ancientcomputing/rc2014/eagle/8085_board/README.md

<b>8085 Processor Board for the RC2014</b>
<p>
Exposes SID/SOD to an FTDI header for UART-less serial.
<p>
Tested. Wiring error between reset RC network and pin 13 of he 74xx14. Fixed in this version.
<p>

<p>
A simple Monitor can be found in the <a href="https://github.com/ancientcomputing/rc2014/tree/master/rom/8085">rom/8085 folder</a>.
<p>
Copyright Ben Chong and licensed freely back to the community.
