ancientcomputing/rc2014/eagle/z80_board/README.md

The board is available from OSH Park at the following link:
<p>

<p>
Copyright Ben Chong and freely licensed back to the community.
