ancientcomputing/rc2014/rom/6502/monitor_ehbasic/README.md

<b>Monitor + EhBASIC ROM</b>
<p>
These are the ROM images that combines the Monitor/Debugger and Enhanced BASIC. This is a 32KB image and can be used to program a 27256 or 28C256. 
<p>
If your ROM address space is only 16KB, you will need to extract the top 16KB of the image to program your device.
<p>
BASIC can be launched by (G)oing to location $c100 from the Monitor. This is the cold start address.
<p>
The BASIC warm start address is at $c103. 
<p>
To return to the Monitor, enter the SYS command.
<p>
<hr>
<p>	
monbas65_16C550.rom : For use with 16550 UART Boards, port address at $c0c0. Will use autoflow control if available. Does not use interrupts with software buffer.
<p>
monbas65_16C550_irq.rom : For use with 16550 UART boards, port address at $c0c0. Does not use autoflow control. Uses interrupts and software buffer.
<p>
monbas65_16c750.rom : For use with 16550 UART RevC board and TI16C750 UART chip (Mouser #1595-TL16C750FN). Uses autoflow control. Does not use interrupts.
<p>
monbas65_6551.rom : For use with 6551 ACIA board. Does not use interrupts. High risk of character overruns at 115200 baud
<p>
monbas65_6850.rom : For use with original RC2014 Serial I/O board with appropriate changes. Does not use interrupts.
<p>
monbas65_rruart.rom : For use with Real Retro UART board. 9600 baud only.
<p>
