ancientcomputing/rc2014/source/z80/rruart/README.md

<b>BIOS for Real Retro UART Board</b>
<p>
This is the BIOS for the Real Retro UART Board using an RCA/Harris CDP6402, AY-3-1015 or similar UART.
<p>
Tested in CPU8080 mode.
