ancientcomputing/rc2014/rom/z80/16x550_revb/README.md

Monitor/Debugger+BASIC for RC2014 system using the 16550 Rev B board.
<p>
The UART port address is c0h instead of 80h.
