ancientcomputing/rc2014/rom/8080_8085/monitor/rruart/README.md

<b>Monitor for 8085 CPU board with Real Retro UART board</b>
<p>
This is the Monitor program for the 8085 CPU Board when using the Real Retro UART Board.
