ancientcomputing/rc2014/eagle/16550_board_rev_b/README.md

16550 UART Board Rev B
<p>
This is the Rev B version of the 16550 UART Board for the RC2014.
<p>
The top 3 changes are:
<br>- Use of port addresses C0H-FFH to avoid collision with the default 68B50 UART
<br>- Use of 74HCT03 open collector gates, particularly to drive the /INT signal line so that it can be shared with other devices that also drive the interrupt line.
<br>- Availability of the 16550's OP1 and OP2 lines to a pin header for general use e.g. to generate an audio signal or page switch RAM/ROM etc.
<p>
This design has been tested with a PC16550CN.
<p>
PCBs are available from OSH Park at:
<p>


<p>
A BIOS will be available soon.
