ancientcomputing/rc2014/eagle/16550_board/README.md

The board has been tested and a BIOS and associated Monitor/Debugger/BASIC binaries released.
<p>
The board is also available from OSH Park at the following link:
<p>

<p>
Note that I do not have any relationship with OSH Park other than that of a customer.
<p>
Copyright Ben Chong and licensed freely back to the community.
