ancientcomputing/rc2014/rom/z80/16x550/README.md

timon.rom - Monitor/Debugger for RC2014 using the 16x550 UART card. Assumes 1.8432MHz oscillator and 115200 baudrate.
<p>
timonbas.rom - Monitor/Debugger+BASIC for RC2014 using the 16x550 UART card. Assumes 1.8432MHz oscillator and 115200 baudrate.
<p>
