ancientcomputing/rc2014/source/6809/bringup/README.MD

Bring-up code for 6809 CPU Board for RC2014.

This code assume the use of the "Real Retro UART" board and will dump a couple of characters ("Ab") to the console.
