ancientcomputing/rc2014/eagle/NSC800_board/rc2014_nsc800.pdf

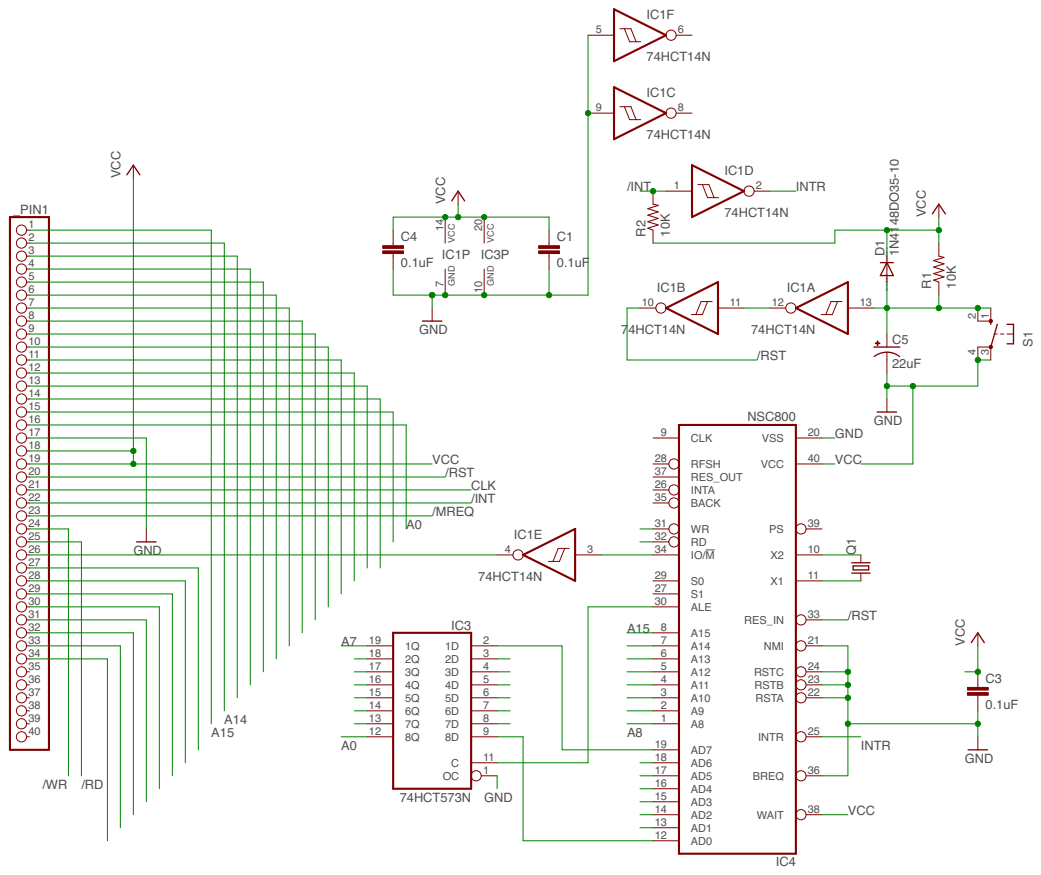
[picture p9: page 1]

SpiceOrder 1 SpiceOrder 2 0.1uF VCC VCC GND 0.1uF VCC GND 0.1uF 22uF 1N4148DO35-10 10K GND VCC 74HCT14N 74HCT14N GND 74HCT14N 74HCT14N 74HCT14N 74HCT14N 74HCT573N 10K NSC800 _PIN1 12345678910111213141516171819202122232425262728293031323334353637383940 C1 C3 C4 S1 3 21 4 C5 D1 R1 IC1A 12 13 IC1B 10 11 IC1PGND VCC 7 14 IC1C 9 8 IC1D 1 2 IC1E 4 3 IC1F 5 6 IC3 OC 1 1D 2 2D 3 3D 4 4D 5 5D 6 6D 7 7D 8 8D 9 C 11 8Q 12 7Q 13 6Q 14 5Q 15 4Q 16 3Q 17 2Q 18 1Q 19 Q1 IC3PGND VCC 10 20 R2 IC4 AD0 12 AD1 13 AD2 14 AD3 15 AD4 16 AD5 17 AD6 18 AD7 19 A8 1 A9 2 A10 3 A11 4 A12 5 A13 6 A14 7 A15 8 ALE 30 S0 29 IO/M 34 RD 32 WR 31 BACK 35 INTA 26 RES_OUT 37 CLK 9 WAIT 38 BREQ 36 INTR 25 RFSH 28 RSTA 22 RSTB 23 RSTC 24 NMI 21 RES_IN 33 X1 11 X2 10 VCC 40 VSS 20 PS 39 S1 27 A7 VCC VCCVCC /RST /RST /RST /INT /INT A0 A0 GND GND /WR A15 A15 A14 A8 CLK /MREQ /RD INTR INTR
