ancientcomputing/rc2014/eagle/rr3kram/rc2014_3kb_ram.pdf

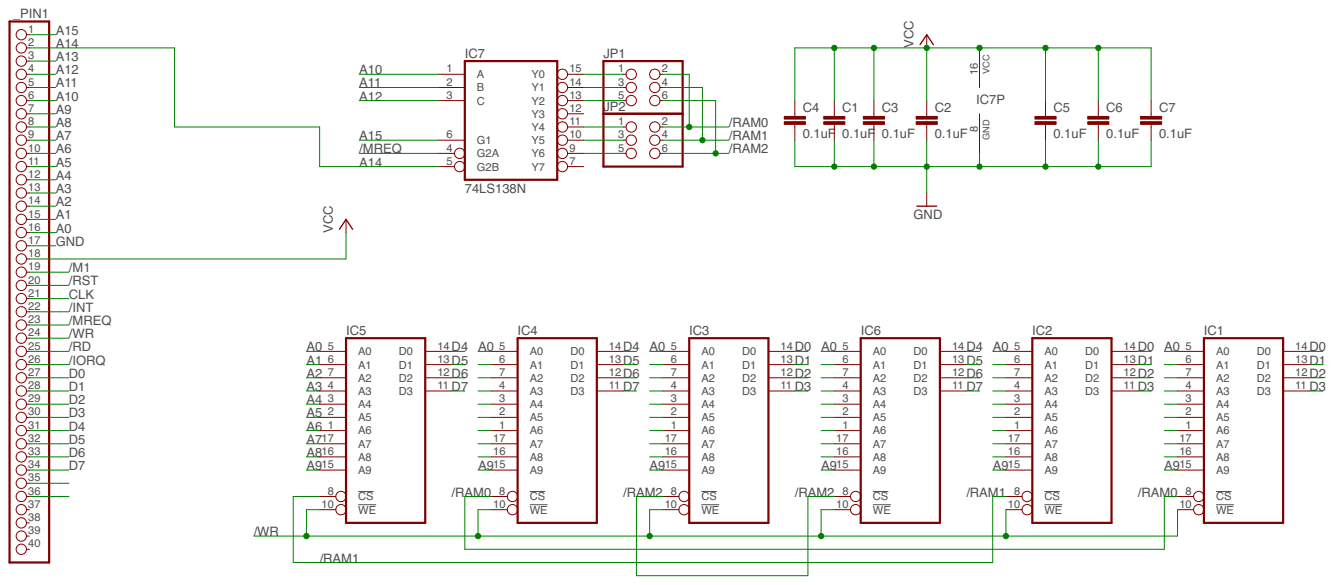
[picture p19: page 1]
