ancientcomputing/rc2014/eagle/6502_board/rc2014_6502.pdf

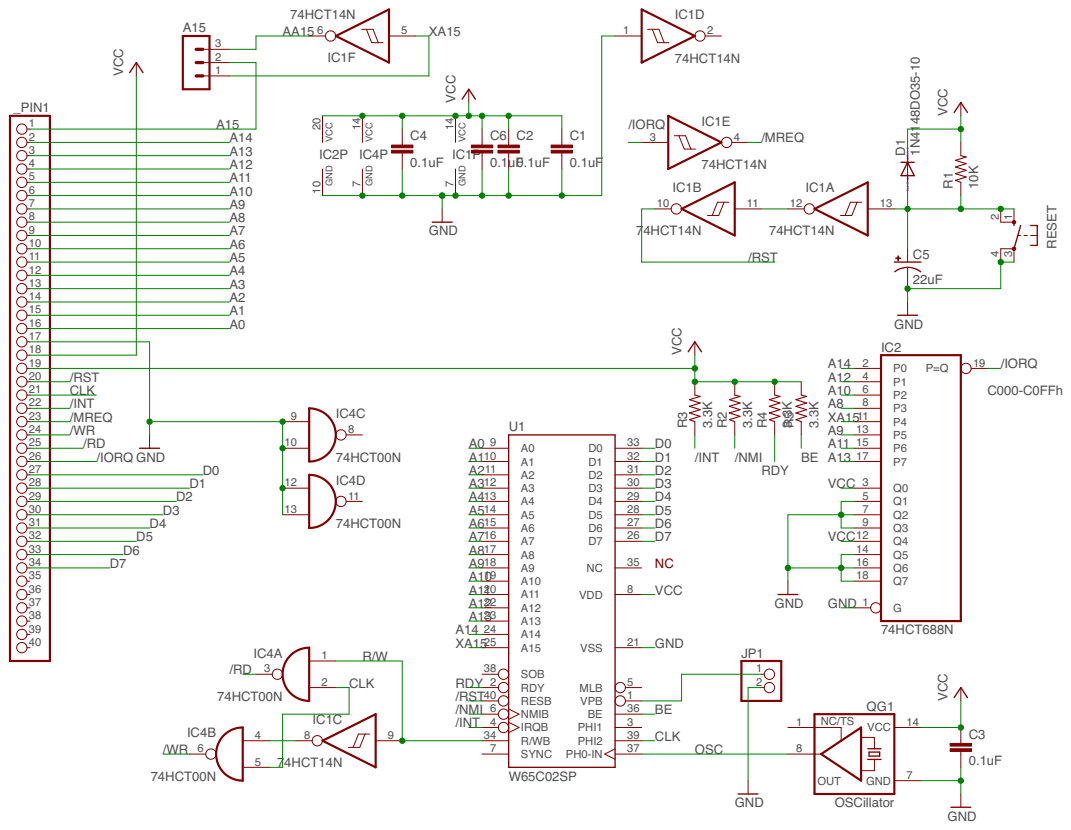
[picture p20: page 1]
