ancientcomputing/rc2014/eagle/16550_board_rev_b/rc2014_16550b.pdf

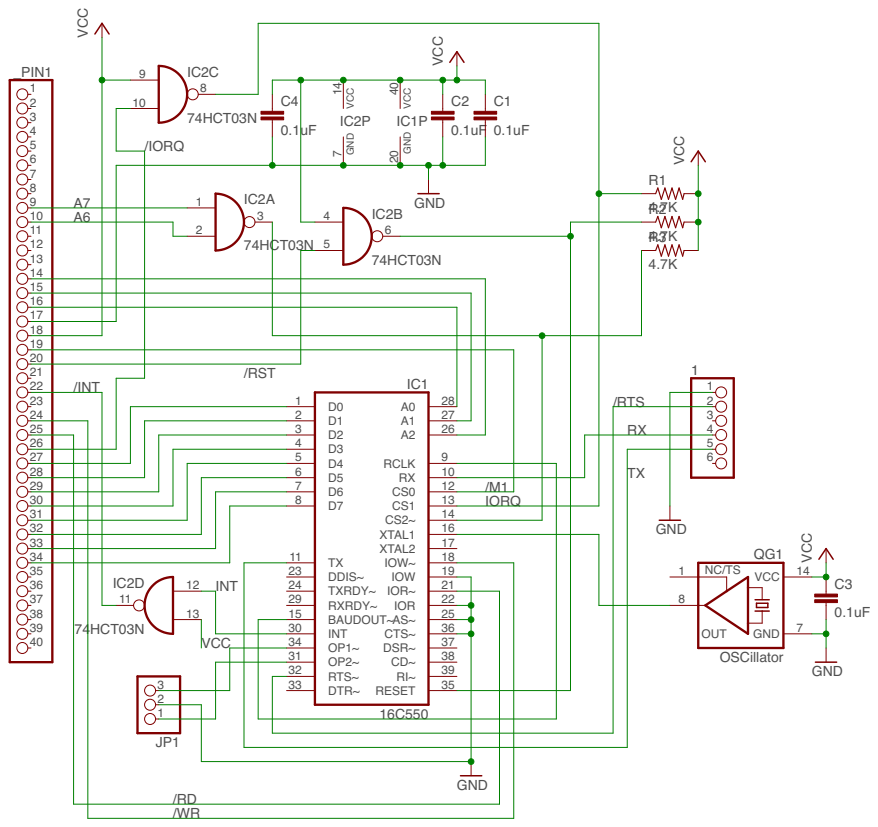
[picture p21: page 1]
