ancientcomputing/rc2014/eagle/16550_board/rc2014_16550.pdf

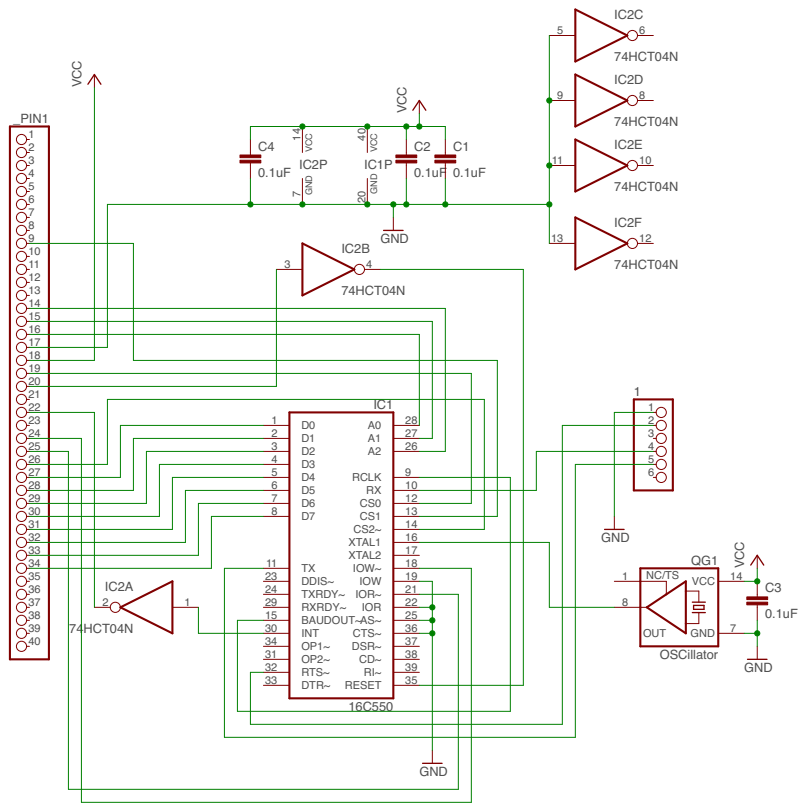
[picture p22: page 1]
