ancientcomputing/rc2014/eagle/rc2014_template.brd

## EAGLE design eagle/rc2014_template.brd (2017-04-10)

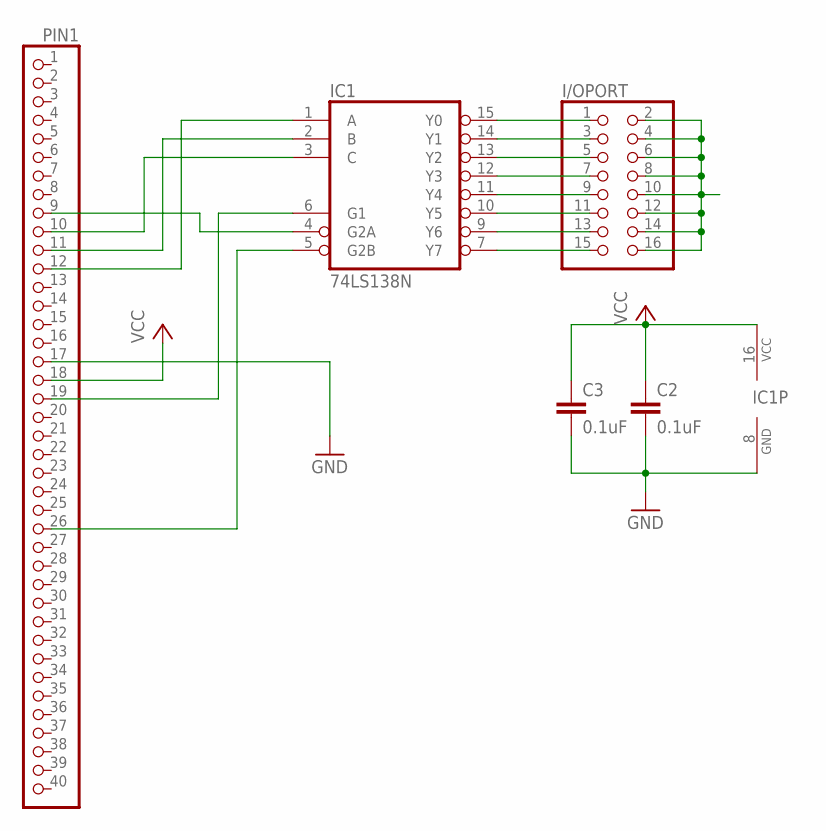
[picture p45: schematic rc2014_template.sch]

Parts:
C2, C3: 0.1uF; C050-024X044
I/OPORT: PINHD-2X8; 2X08
IC1: 74LS138N; DIL16
PIN1: PINHD-1X40; 1X40

Connections:
GND: C2.2, C3.2, IC1.8 (GND), PIN1.17
unnamed: IC1.6 (G1), PIN1.19
unnamed: IC1.5 (G2B), PIN1.26
unnamed: IC1.4 (G2A), PIN1.9
unnamed: IC1.3 (C), PIN1.10
unnamed: IC1.2 (B), PIN1.11
unnamed: IC1.1 (A), PIN1.12
unnamed: I/OPORT.1, IC1.15 (Y0)
unnamed: I/OPORT.3, IC1.14 (Y1)
unnamed: I/OPORT.5, IC1.13 (Y2)
unnamed: I/OPORT.7, IC1.12 (Y3)
unnamed: I/OPORT.9, IC1.11 (Y4)
unnamed: I/OPORT.11, IC1.10 (Y5)
unnamed: I/OPORT.13, IC1.9 (Y6)
unnamed: I/OPORT.15, IC1.7 (Y7)
unnamed: I/OPORT.2, I/OPORT.4, I/OPORT.6, I/OPORT.8, I/OPORT.10, I/OPORT.12, I/OPORT.14, I/OPORT.16
VCC: C2.1, C3.1, IC1.16 (VCC), PIN1.18

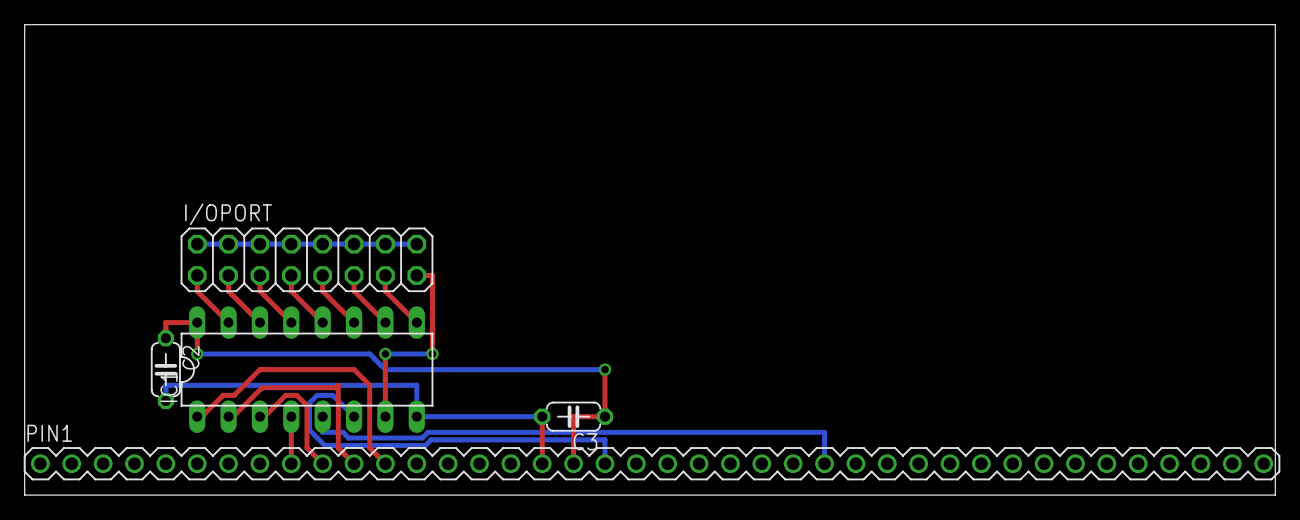
[picture p46: board rc2014_template.brd from above]

Board: 2 copper layers, 101.3 x 38.1 mm, 5 parts (0 on the bottom side), 17 nets.
