ancientcomputing/rc2014/source/6502/monitor/16c750.asm

; 6502 BIOS 
; Based on original code by Daryl Rictor
; Adapted to use a 16C750 UART with the RevC board for RC2014
; Renamed to 16c750.asm
;
; Note: Assumes the use of a 16C750 with autoflow control and 64-char buffers
;
; ----------------- assembly instructions ---------------------------- 
;
; this is a subroutine library only
; it must be included in an executable source file
;
;
;*** I/O Locations *******************************
; Define the i/o address of the UART chip
;*** 16C750 UART ************************

uart_base       = $c0c0
uart_reg0       = $c0c0
uart_reg1       = $c0c1
uart_reg2       = $c0c2
uart_reg3       = $c0c3
uart_reg4       = $c0c4
uart_reg5       = $c0c5
uart_reg6       = $c0c6
uart_reg7       = $c0c7
uart_xmit       = uart_reg0     ; Used by upload.asm

;
;***********************************************************************
; UART I/O Support Routines
; We'll use Daryl's routine names for compatibility with his software/code
; Otherwise, we'll use UART-agnostic nomemclature

;---------------------------------------------------------------------
;
 
ACIA1_init
uart_init
                lda     #>uart_irq
                ldx     #<uart_irq
                stx      irq_vector
                sta      irq_vector+1
                lda     #$80            ; Line control register, Set DLAB=1
                sta     uart_reg3
                lda     #$01            ; 115200 with 1.8432MHz;  OSC / (16 * Baudrate)
                sta     uart_reg0       ; Divisor latch
                lda     #$00
                sta     uart_reg1       ; Divisor latch
                lda     #$03            ; Line control register, 8N1, DLAB=0
                sta     uart_reg3
                lda     #$02            ; Modem control register
                sta     uart_reg4       ; Enable RTS
                lda     #$a7            ; FIFO enable, reset RCVR/XMIT FIFO, 64-char
                sta     uart_reg2
;                lda     #$01            ; Enable receiver interrupt
;                sta     uart_reg1
                jsr     AFE_16C550      ; Enable auto flow control
                
                lda     uart_reg3            ; Line control register, Set DLAB=1
                ora     #$80
                sta     uart_reg3
                lda     #$a1           ; FIFO enable, 64-char
                sta     uart_reg2
                lda     uart_reg3            ; Line control register, 8N1, DLAB=0
                and     #$7f
                sta     uart_reg3


                rts                     ; done
                
;---------------------------------------------------------------------
; Input char from UART (blocking)
; Exit: character in A
ACIA1_Input
uart_input

               lda      uart_reg5           ; Serial port status             
               and      #$01               ; is recvr full
               beq      uart_input        ; no char to get
               lda      uart_reg0           ; get chr
               rts                      ;

;---------------------------------------------------------------------
; Non-waiting get character routine 
; Scan for input (no wait), C=1 char, C=0 no character
ACIA1_Scan
uart_scan
                clc
                lda   uart_reg5        ; Serial port status
                and   #$01               ; mask rcvr full bit
                beq   uart_scan2
                lda   uart_reg0           ; get chr
                sec
uart_scan2     rts

;---------------------------------------------------------------------
; output to OutPut Port
; Entry: character in A
; Exit: character in A
ACIA1_Output
uart_output   
                pha                      ; save registers
uart_out1     
                lda   uart_reg5           ; serial port status
                and   #$20               ; is tx buffer empty
                beq   uart_out1         ; no
                pla                      ; get chr
                sta   uart_reg0           ; put character to Port
                rts                      ; done

;---------------------------------------------------------------------
; Enable autoflow control
AFE_16C550
                LDA     #$87                  ; Trigger level, FIFO enable, reset FIFO
                sta     uart_reg2
                ; Use this to enable autoflow control
                LDA     #$22                  ; Modem control register
                sta     uart_reg4    ; Enable AFE
                rts

;---------------------------------------------------------------------
uart_irq

                jmp     null_irq

;
;end of file
